ptsfdtz/Remote-control-handle/image/4.png

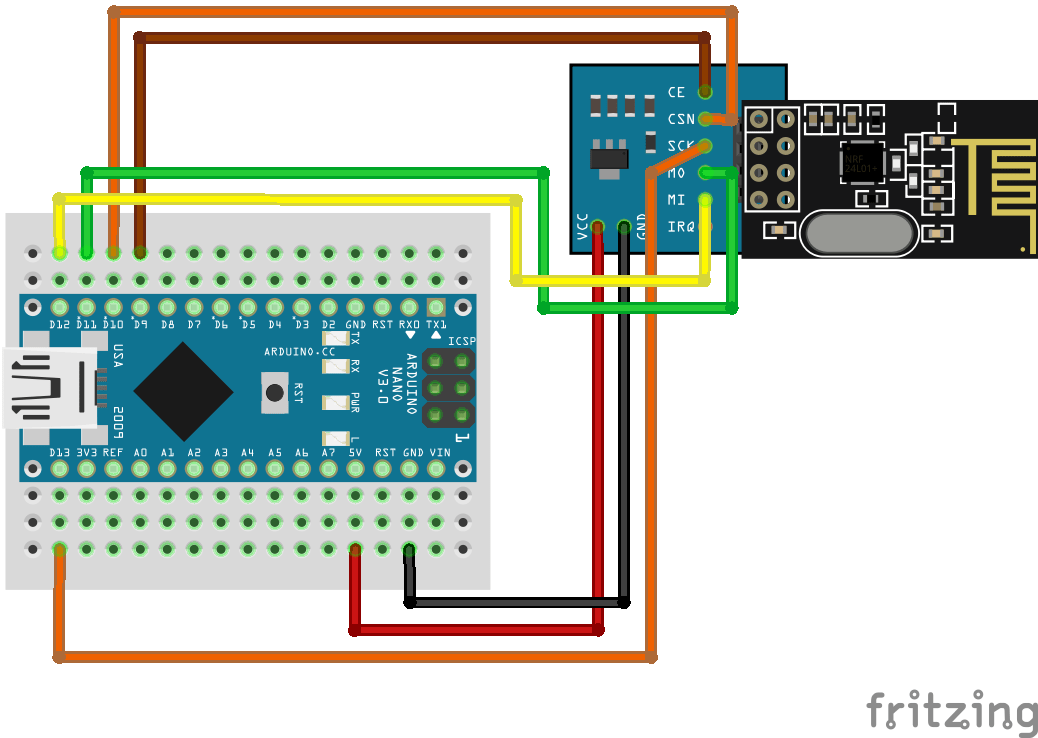
image/4.png
