ptsfdtz/Remote-control-handle/part/NRF24+SMA/User Library-NRF24+SMA_6RFX.SLDPRT

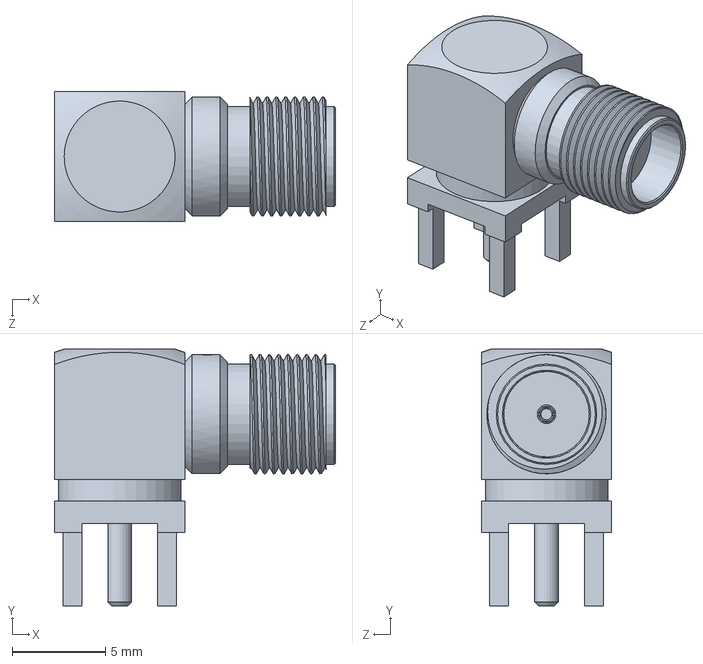
[picture p24: CAD file, 2023-12-04]
part/NRF24+SMA/User Library-NRF24+SMA_6RFX.SLDPRT
15.1 x 13.8 x 7.00 mm
