ptsfdtz/Remote-control-handle/part/握把.SLDPRT

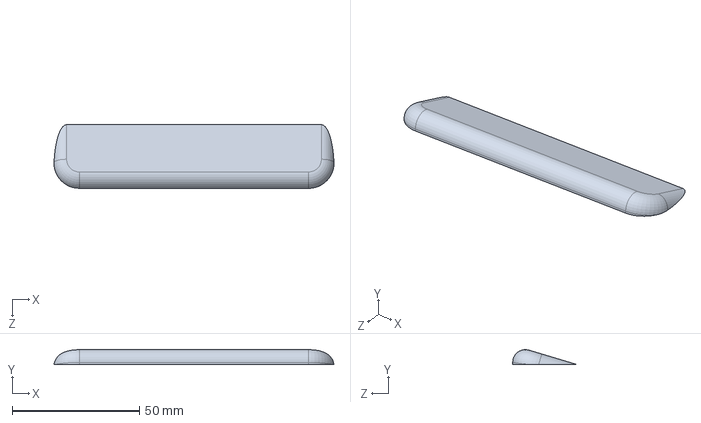
[picture p25: CAD file, 2024-01-29]
part/握把.SLDPRT
109.9 x 5.76 x 25.0 mm
