ptsfdtz/Remote-control-handle/part/Backplate.SLDPRT

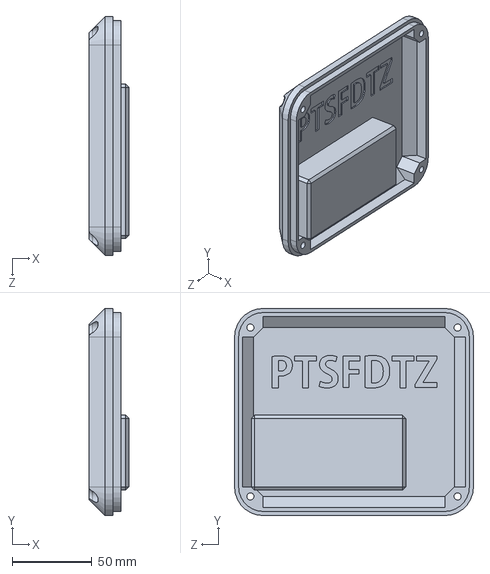
[picture p26: CAD file, 2023-12-06]
part/Backplate.SLDPRT
25.0 x 130.0 x 150.0 mm
