ptsfdtz/Remote-control-handle/part/NRF24+SMA/User Library-NRF24+SMA_SMA Antenna.SLDPRT

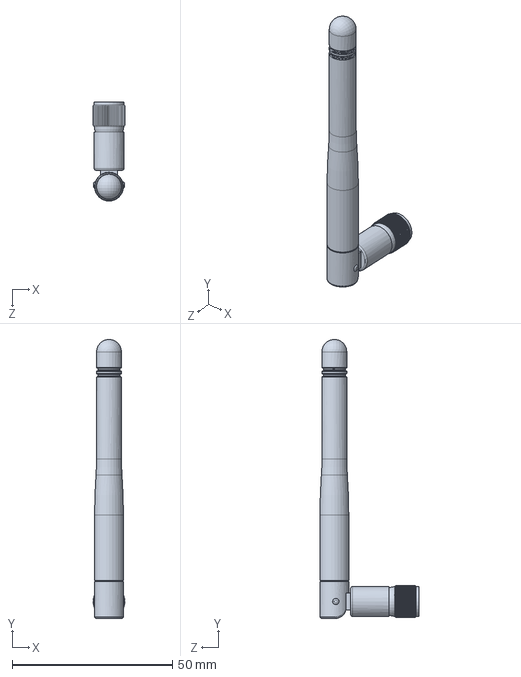
[picture p27: CAD file, 2023-12-04]
part/NRF24+SMA/User Library-NRF24+SMA_SMA Antenna.SLDPRT
10.00 x 86.9 x 30.9 mm
