ptsfdtz/Remote-control-handle/part/rocker.SLDPRT

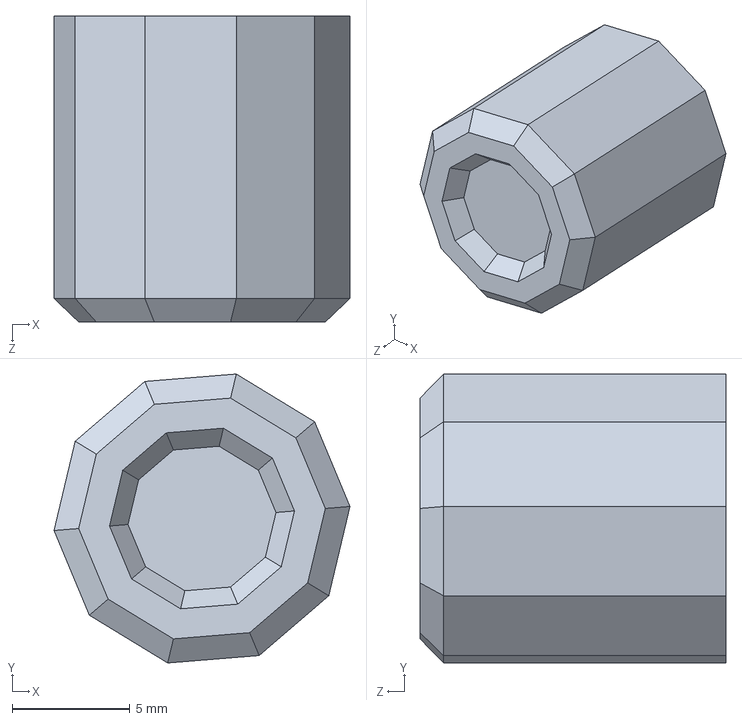
[picture p28: CAD file, 2023-12-05]
part/rocker.SLDPRT
12.6 x 12.3 x 13.0 mm
