ptsfdtz/Remote-control-handle/part/Battery backplane.SLDPRT

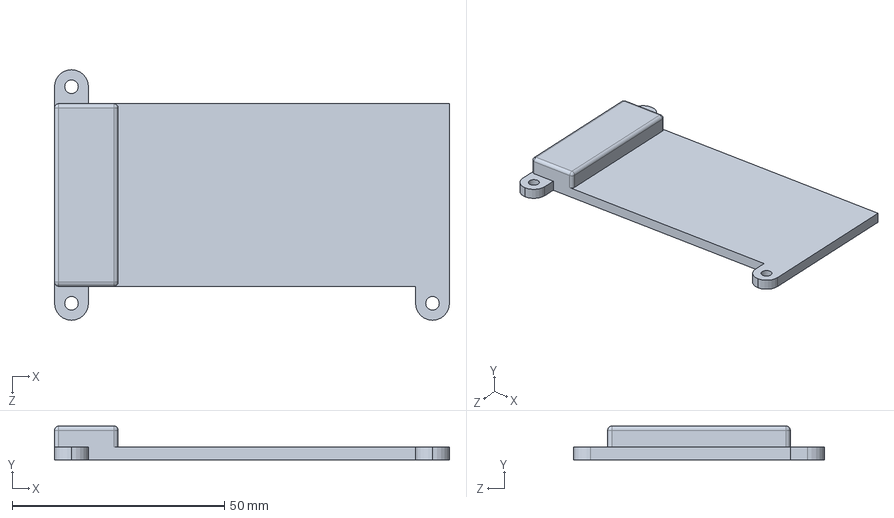
[picture p29: CAD file, 2023-12-04]
part/Battery backplane.SLDPRT
93.0 x 8.00 x 59.0 mm
