ptsfdtz/Remote-control-handle/part/NRF24+SMA/User Library-NRF24+SMA_User Library-PLD-8.SLDPRT

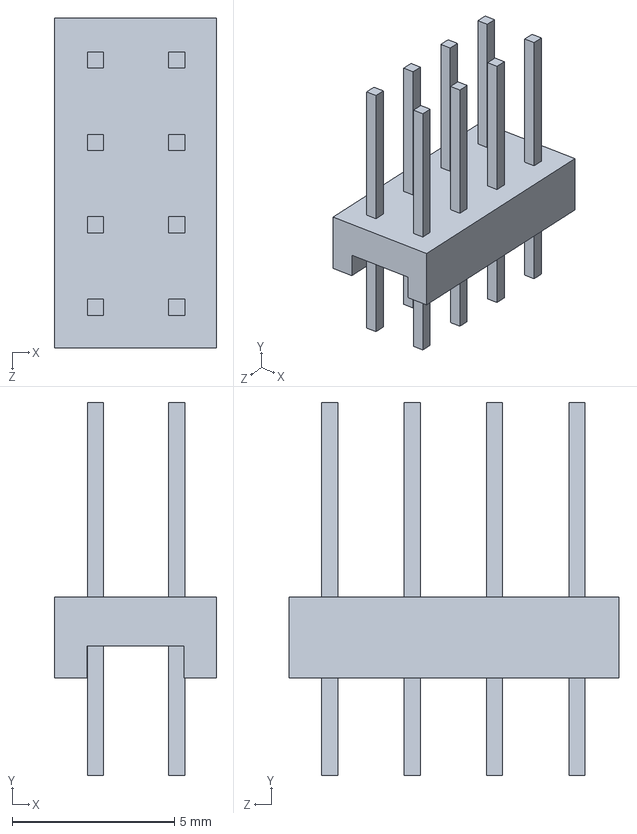
[picture p30: CAD file, 2023-12-04]
part/NRF24+SMA/User Library-NRF24+SMA_User Library-PLD-8.SLDPRT
5.00 x 11.5 x 10.2 mm
