ptsfdtz/Remote-control-handle/part/Battery-compartment.SLDPRT

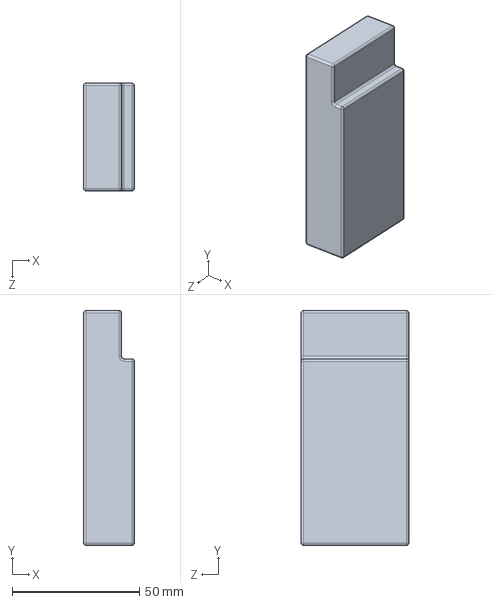
[picture p31: CAD file, 2023-12-04]
part/Battery-compartment.SLDPRT
20.0 x 92.5 x 42.5 mm
