ptsfdtz/Remote-control-handle/part/button.SLDPRT

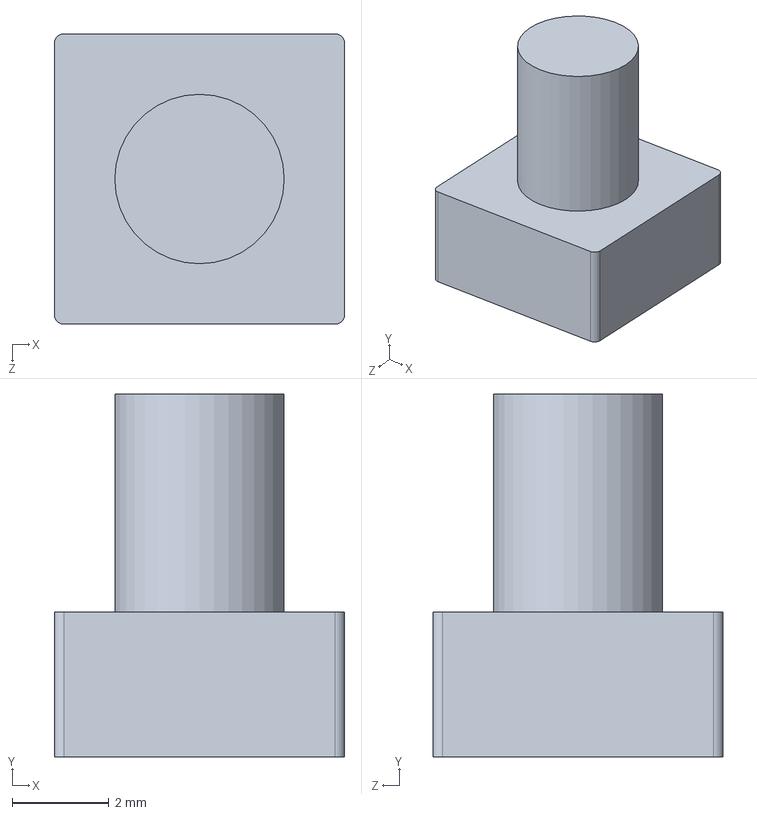
[picture p32: CAD file, 2023-12-04]
part/button.SLDPRT
6.00 x 7.50 x 6.00 mm
