ptsfdtz/Remote-control-handle/part/EC11B15244/User Library-EC11B15244_Shaft.sldprt

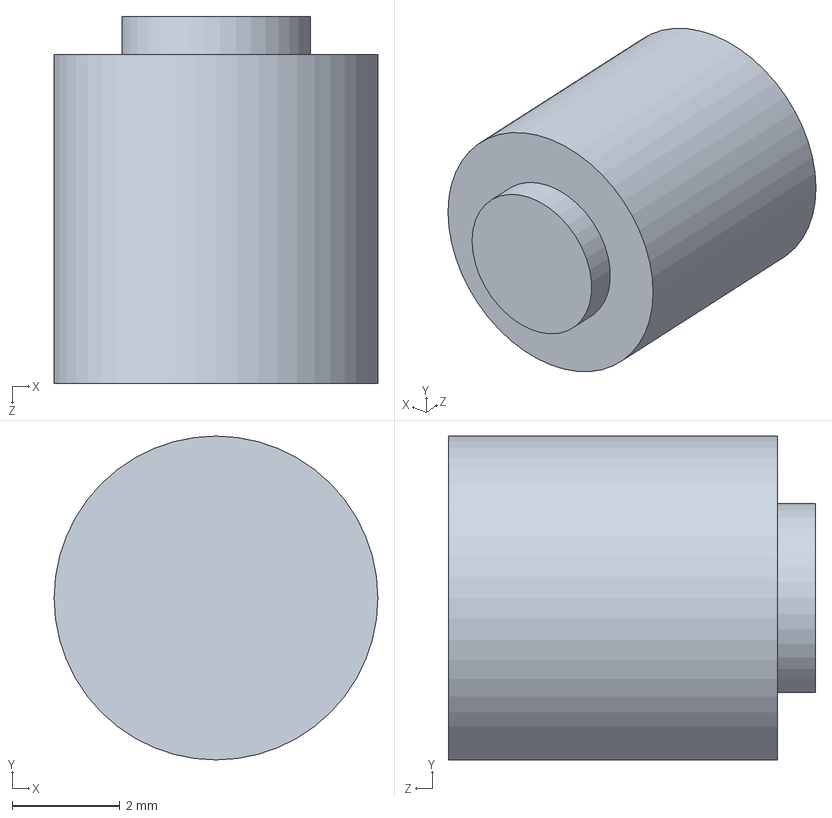
[picture p33: CAD file, 2023-12-04]
part/EC11B15244/User Library-EC11B15244_Shaft.sldprt
6.00 x 6.00 x 6.80 mm
