ptsfdtz/Remote-control-handle/part/ps2-pcb.SLDPRT

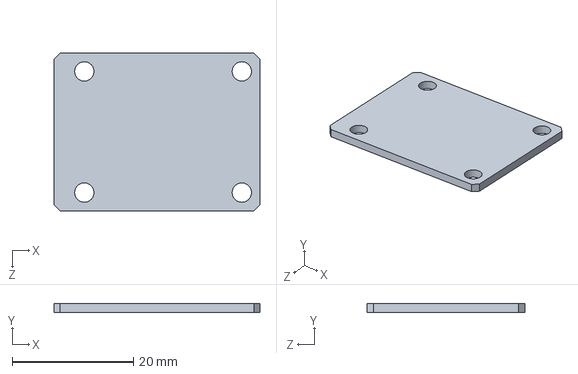
[picture p34: CAD file, 2023-12-04]
part/ps2-pcb.SLDPRT
34.0 x 1.50 x 26.0 mm
